Pr1neeth/Active-Thrust-Vector-Controlled-Rocket/Avionics/CAM Files/1.sch

## EAGLE design Avionics/CAM Files/1.sch (2025-09-09)

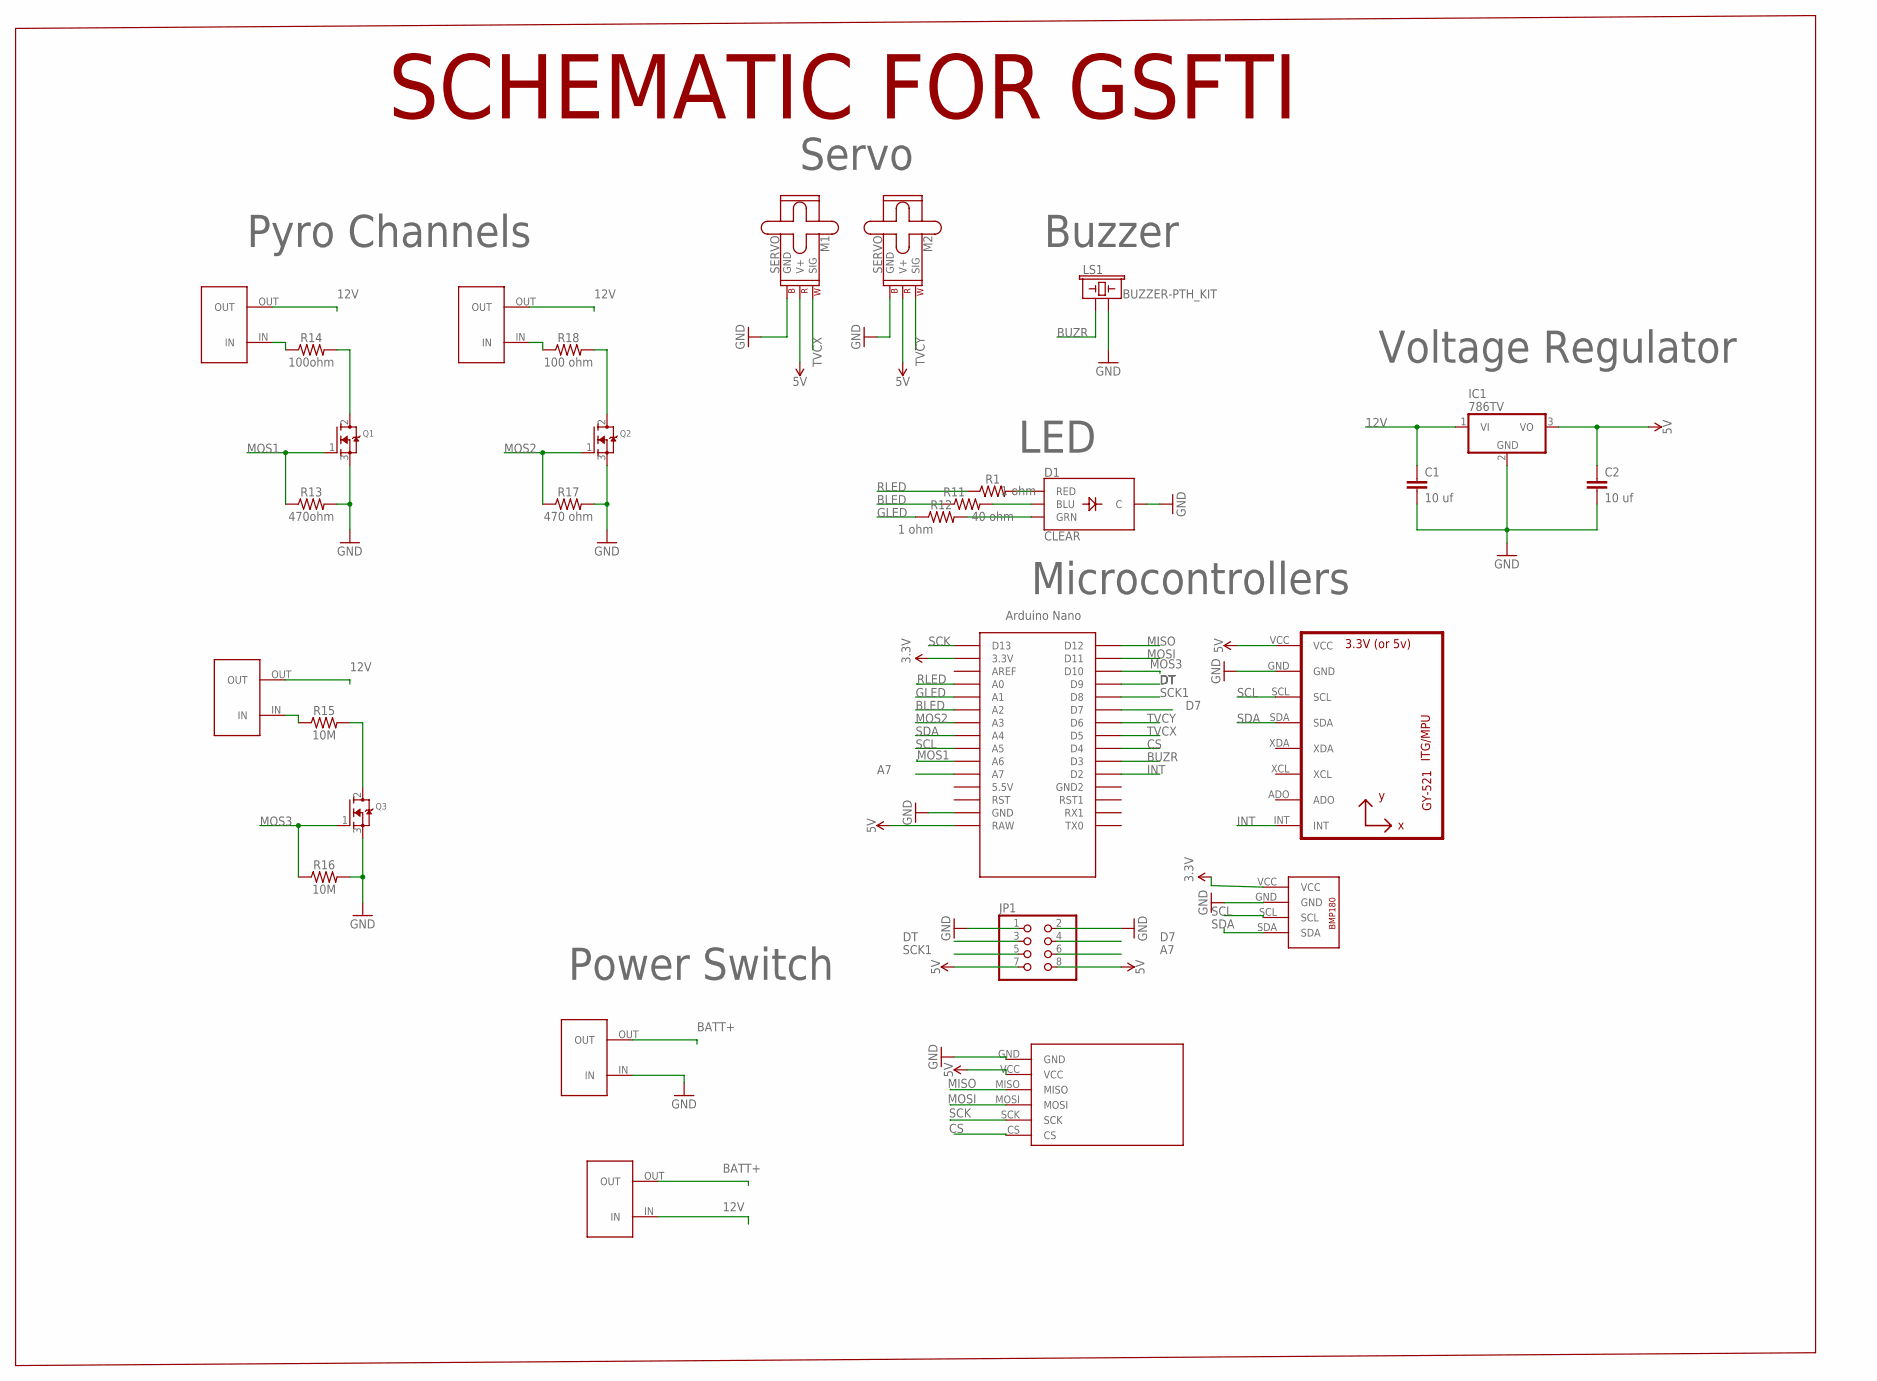
[picture p6: schematic 1.sch]

Parts:
C1, C2: 10 uf; C2.5-3
D1: CLEAR; LED-RGB-THRU
IC1: 786TV; TO220V
JP1: PINHD-2X4; 2X04
LS1: BUZZER-PTH_KIT; BUZZER-12MM-KIT
M1, M2: SERVO; 1X03
Q1, Q2, Q3: MOSFET-NGDS_TO220V; TO220V
R1, R12: 1 ohm; AXIAL-0.3
R11: 40 ohm; AXIAL-0.3
R13: 470ohm; AXIAL-0.3
R14: 100ohm; AXIAL-0.3
R15, R16: 10M; AXIAL-0.3
R17: 470 ohm; AXIAL-0.3
R18: 100 ohm; AXIAL-0.3
U1: GY-521MPU6050; GY-521
U$1: NANO
U$2: BMP180
U$3: SD
U$4, U$7, U$8, U$9, U$10: TERMINALBLOCKS

Connections:
3.3V: U$1.3.3V, U$2.VCC
5V: C2.1, IC1.3 (VO), JP1.7, JP1.8, M1.2 (V+), M2.2 (V+), U1.VCC, U$1.RAW, U$3.VCC
12V: C1.1, IC1.1 (VI), U$7.IN, U$8.OUT, U$9.OUT, U$10.OUT
A7: JP1.6, U$1.A7
BATT+: U$4.OUT, U$7.OUT
BLED: R11.P$1 (1), U$1.A2
BUZR: LS1.+ (1), U$1.D3
CS: U$1.D4, U$3.CS
D7: JP1.4, U$1.D7
DT: JP1.3, U$1.D9
GLED: R12.P$1 (1), U$1.A1
GND: C1.2, C2.2, D1.2 (C), IC1.2 (GND), JP1.1, JP1.2, LS1.- (2), M1.3 (GND), M2.3 (GND), Q1.3 (S), Q2.3 (S), Q3.3 (S), R13.P$2 (2), R16.P$2 (2), R17.P$2 (2), U1.GND, U$1.GND, U$2.GND, U$3.GND, U$4.IN
INT: U1.INT, U$1.D2
MISO: U$1.D12, U$3.MISO
MOS1: Q1.1 (G), R13.P$1 (1), U$1.A6
MOS2: Q2.1 (G), R17.P$1 (1), U$1.A3
MOS3: Q3.1 (G), R16.P$1 (1), U$1.D10
MOSI: U$1.D11, U$3.MOSI
unnamed: D1.1 (RED), R1.P$2 (2)
unnamed: D1.4 (BLU), R11.P$2 (2)
unnamed: D1.3 (GRN), R12.P$2 (2)
unnamed: Q2.2 (D), R18.P$2 (2)
unnamed: R18.P$1 (1), U$9.IN
unnamed: Q1.2 (D), R14.P$2 (2)
unnamed: R14.P$1 (1), U$8.IN
unnamed: Q3.2 (D), R15.P$2 (2)
unnamed: R15.P$1 (1), U$10.IN
RLED: R1.P$1 (1), U$1.A0
SCK: U$1.D13, U$3.SCK
SCK1: JP1.5, U$1.D8
SCL: U1.SCL, U$1.A5, U$2.SCL
SDA: U1.SDA, U$1.A4, U$2.SDA
TVCX: M1.1 (SIG), U$1.D5
TVCY: M2.1 (SIG), U$1.D6

Notes on the sheet:
Pyro Channels
Servo
Buzzer
Voltage Regulator
LED
Microcontrollers
Power Switch
SCHEMATIC FOR GSFTI
